oxidecomputer/hw-k2/mech_model/U2_conn_cutout.DXF

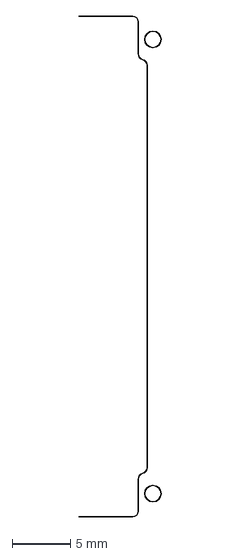
[picture p17: CAD file, 2022-11-04]
mech_model/U2_conn_cutout.DXF
7.05 x 43.0 mm
