oxidecomputer/hw-k2/mech_model/Part2.SLDPRT

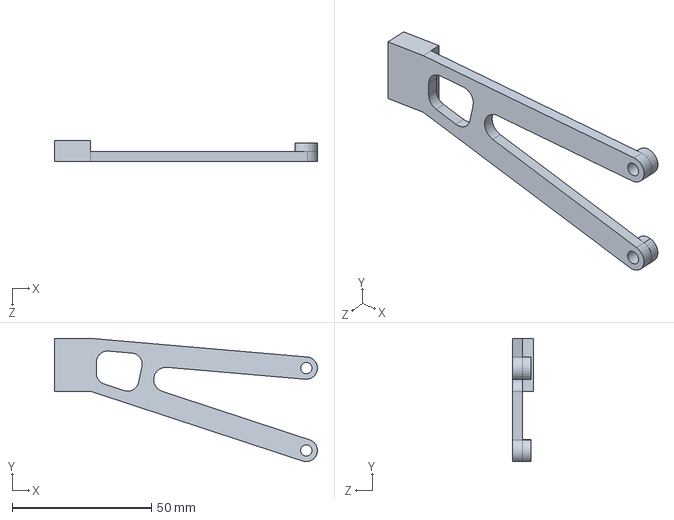
[picture p18: CAD file, 2022-11-04]
mech_model/Part2.SLDPRT
94.3 x 44.2 x 7.38 mm
